leomil72/LM80C/Schematics/LM80C 64K/Kicad/LM80C 64K.sch

## KiCad design Schematics/LM80C 64K/Kicad/LM80C 64K.sch (2021-03-08)

Schematic: LM80C 64K.sch

Parts:
C1, C2, C3, C4, C8, C9, C10, C12, C13, C16, C17, C19, C20, C21, C22, C23, C24, C25, C26, C27, C28, C29, C30, C32, C33, C37, C42: 0.1u; C_Disc_D5.0mm_W2.5mm_P2.50mm
C14, C15: 33p; C_Disc_D5.0mm_W2.5mm_P2.50mm
C18: 220u; CP_Radial_D10.0mm_P2.50mm
C31: 100u; CP_Radial_D5.0mm_P2.00mm
C34, C35: 22p; C_Disc_D5.0mm_W2.5mm_P2.50mm
C36: 100n; C_Disc_D5.0mm_W2.5mm_P2.50mm
C38, C39: 100u; CP_Radial_D4.0mm_P2.00mm
C40, C41: 10u; CP_Radial_D5.0mm_P2.00mm
D1, D3, D5: LED; LED_D5.0mm
D2, D4: 1N4007; D_DO-41_SOD81_P10.16mm_Horizontal
FB1: Ferrite_Bead; LairdTech_28C0236-0JW-10
H1, H2, H3, H4: MountingHole_Pad; MountingHole_3.2mm_M3_Pad
J1: Conn_02x20_Odd_Even; PinHeader_2x20_P2.54mm_Vertical
J2: AV-VIDEO; RCAsimple
J3: Conn_01x03; PinHeader_1x03_P2.54mm_Vertical
J4: Conn_01x12; PinHeader_1x12_P2.54mm_Vertical
J5, J6: Conn_01x08_Male; PinHeader_1x08_P2.54mm_Vertical
J7, J12: FT232 CONN; PinSocket_1x06_P2.54mm_Vertical
J8: Barrel_Jack_Switch; BarrelJack_Horizontal
J9: Conn_01x20; PinHeader_1x20_P2.54mm_Vertical
J10: AV-L AUDIO; RCAsimple
J11: AV-R AUDIO; RCAsimple
JP1: Jumper; PinHeader_1x02_P2.54mm_Vertical
Q1: 2N3904; TO-92_Inline
Q2: BC337; TO-92_Inline
R1, R2, R6, R8, R11, R20, R21, R22, R31, R34, R36, R37, R51: 10K; R_Axial_DIN0207_L6.3mm_D2.5mm_P10.16mm_Horizontal
R3, R5, R32, R33, R35, R48, R49, R55, R56: 2K7; R_Axial_DIN0207_L6.3mm_D2.5mm_P10.16mm_Horizontal
R4, R38, R41, R44, R46, R47, R53: 1K; R_Axial_DIN0207_L6.3mm_D2.5mm_P10.16mm_Horizontal
R7: 470R; R_Axial_DIN0207_L6.3mm_D2.5mm_P10.16mm_Horizontal
R9, R10: 75R; R_Axial_DIN0207_L6.3mm_D2.5mm_P10.16mm_Horizontal
R12, R13, R14, R15, R16, R17, R18, R19: 390R; R_Axial_DIN0207_L6.3mm_D2.5mm_P10.16mm_Horizontal
R23, R24, R25, R26, R27, R28, R29, R30, R54: 330R; R_Axial_DIN0207_L6.3mm_D2.5mm_P10.16mm_Horizontal
R39: 100K; R_Axial_DIN0207_L6.3mm_D2.5mm_P10.16mm_Horizontal
R40: 8M2; R_Axial_DIN0207_L6.3mm_D2.5mm_P10.16mm_Horizontal
R42, R43: 2K2; R_Axial_DIN0207_L6.3mm_D2.5mm_P10.16mm_Horizontal
R45: 330; R_Axial_DIN0207_L6.3mm_D2.5mm_P10.16mm_Horizontal
R50: 47K; R_Axial_DIN0207_L6.3mm_D2.5mm_P10.16mm_Horizontal
R52: 470; R_Axial_DIN0207_L6.3mm_D2.5mm_P10.16mm_Horizontal
SW1: SW_DIP_x01; SW_PUSH_6mm_H4.3mm
U1: 74HCT139; DIP-16_W7.62mm_LongPads
U2: 74HCT138; DIP-16_W7.62mm_LongPads
U3, U22: 74HCT32; DIP-14_W7.62mm_LongPads
U5: Z80-CPU; DIP-40_W15.24mm_LongPads
U6, U7: HM62256BLP-12; DIP-28_W15.24mm_LongPads
U9: 28C256; DIP-28_W15.24mm_LongPads
U10: 74HCT08; DIP-14_W7.62mm_LongPads
U11: Z80-CTC; DIP-28_W15.24mm_LongPads
U12: Z80-PIO; DIP-40_W15.24mm_LongPads
U13: TMS9918A; DIP-40_W15.24mm_LongPads
U14, U15, U16: 74HCT574; DIP-20_W7.62mm_LongPads
U17: ULN2803A; DIP-18_W7.62mm_LongPads
U18: Z80-SIO_0; DIP-40_W15.24mm_LongPads
U19, U23: 74HCT04; DIP-14_W7.62mm_LongPads
U20: HM62256BLP-7; DIP-28_W15.24mm_LongPads
U21: 4066; DIP-14_W7.62mm_LongPads
U24: 74HC02; DIP-14_W7.62mm_LongPads
U25: AY-3-8910; DIP-40_W15.24mm_LongPads
U26: LM317_3PinPackage; TO-220-3_Vertical
U27: NE555P; DIP-8_W7.62mm
U28: 74HCT74; DIP-14_W7.62mm_LongPads
Y1: 10.738635MHz; Crystal_HC49-4H_Vertical
Y2: 7.372800MHz; Crystal_HC49-4H_Vertical

Notes on the sheet:
CLOCK DIVIDER /2: SYSTEM CLOCK IS 3.686400 MHz
POWER REGULATOR (9-12V IN --> 5V OUT)
6: DTR 5: RX 4: TX 3: VCC 2: CTS 1: GND
WARNING! VDP DATA BUS HAS CD0 AS MSB AND CD7 AS LSB!
BE CAREFUL!! VAxx CONNECTIONS BETWEEN D-FFs AND SRAM DON’T FOLLOW THE NUMERICAL ORDER!
COMPOSITE VIDEO OUT
I/O DECODER: 0000xxxx: PIO 0001xxxx: CTC 0010xxxx: SIO 0011xxxx: VDP 0100xxxx: PSG 0101xxxx: CF
CLOCK DIVIDER: CLK2 = 1.832400MHz
Connect to an 8-segment LED bar graph or to 8x LEDs.
MANUAL RESET
Keyboard connector
PSG ADDRESS DECODER: 0100xx00: READ FROM PSG (IN) 0100xx01: WRITE TO PSG (OUT) 0100xx00: LATCH ADDRESS (OUT)
RAM/ROM SELECTOR
Cap values are NOT valid for every crystal. Check the load capacitance of yours
POWER LED
RESET CIRCUIT (0.5s TRIGGER TIME)
SPECIAL FUNCTIONS: PB0: switch for ROM/RAM on bank#1 PB1: switch between bansk #0/1 on VRAM PB4: serial 1 error (disables serial switch) PB6: serial 1 opened (enables serial switch)
NOTE: not implemented in code yet
CONNECT IF YOUR CF/IDE ADAPTER DOES NOT HAVE A BUILT-IN ACTIVITY LED
CF ADAPTER POWER JACK
