leomil72/LM80C/BASIC examples/amiga_hand.bas

10 REM AMIGA BOOT HAND
20 REM WRITTEN BY
30 REM ANTONINO PORCINO 
40 REM 01 OCTOBER 2021
50 REM ORIGINAL SOURCE 
60 REM TAKEN SOMEWHERE 
70 REM FROM INTERNET
80 REM
100 SCREEN 2
200 COLOR 1,15,5
1000 PLOT 107,35
1001 DRAW 107,35,130,35
1002 DRAW 130,35,130,57
1003 DRAW 130,57,185,57
1004 DRAW 185,57,185,35
1005 DRAW 185,35,197,35
1006 DRAW 197,35,208,46
1007 DRAW 208,46,208,118
1008 DRAW 208,118,199,118
1009 DRAW 199,118,199,80
1010 DRAW 199,80,136,80
1011 DRAW 136,80,134,78
1012 DRAW 134,78,125,78
1013 DRAW 125,78,124,80
1014 DRAW 124,80,117,80
1015 DRAW 117,80,117,89
1016 DRAW 117,89,107,96
1017 DRAW 107,96,107,35
1018 REM PAINT 109,93
1019 PLOT 105,96
1020 DRAW 105,96,105,34
1021 DRAW 105,34,198,34
1022 DRAW 198,34,210,46
1023 DRAW 210,46,210,119
1024 DRAW 210,119,158,119
1025 DRAW 158,119,158,124
1026 DRAW 158,124,154,132
1027 DRAW 154,132,150,137
1028 DRAW 150,137,146,140
1029 DRAW 146,140,140,149
1030 DRAW 140,149,132,153
1031 DRAW 132,153,132,164
1032 DRAW 132,164,82,164
1033 DRAW 82,164,82,133
1034 DRAW 82,133,81,133
1035 DRAW 81,133,81,105
1036 DRAW 81,105,85,99
1037 DRAW 85,99,92,93
1038 DRAW 92,93,93,89
1039 DRAW 93,89,97,82
1040 DRAW 97,82,102,79
1041 DRAW 102,79,105,78
1042 DRAW 105,78,105,78
1043 DRAW 105,78,102,80
1044 DRAW 102,80,98,82
1045 DRAW 98,82,94,89
1046 DRAW 94,89,93,93
1047 DRAW 93,93,86,99
1048 DRAW 86,99,82,105
1049 DRAW 82,105,82,132
1050 DRAW 82,132,83,133
1051 DRAW 83,133,83,163
1052 DRAW 83,163,112,163
1053 DRAW 112,163,112,142
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
1167 DRAW 126,125,126,128
1168 PLOT 198,35
1169 DRAW 198,35,209,46
1170 DRAW 209,46,209,118
1171 PAINT 106,35
1172 PAINT 131,35
1173 PAINT 169,39
1174 PAINT 178,51
1175 PAINT 184,39
1176 PAINT 198,118
1177 PAINT 147,120
1178 PAINT 118,81
1200 GPRINT "LM80C",18,12,4
2000 GOTO 2000
