leomil72/LM80C/BASIC examples/graphic_demos.bas

10 A=INKEY(10)
20 SCREEN 2:GPRINT "Press any key for next demo...",1,23
30 DRAW 127,95,RND(1)*256,RND(1)*192,RND(1)*13+1
40 IF INKEY(0)=0 THEN 30
70 CLS:GPRINT "Press RUN/STOP to stop",5,23,15,1
80 FOR I=0 TO 255
90 DRAW 127,95,I,0,RND(1)*13+1:NEXT
100 FOR I=0 TO 191:
110 DRAW 127,95,255,I,RND(1)*13+1:NEXT
120 FOR I=255 TO 0 STEP -1
130 DRAW 127,95,I,191,RND(1)*13+1:NEXT
140 FOR I=191 TO 0 STEP -1
150 DRAW 127,95,0,I,RND(1)*13+1:NEXT
160 GPRINT "Press any key to exit",5,23,1,15
170 A=INKEY(5):IF A=0 THEN 170
180 SCREEN 1
