leomil72/LM80C/BASIC examples/graphic_examples.bas

5 REM GRAPHIC EXAMPLES
6 REM FOR LM80C BASIC
7 REM WRITTEN BY LEONARDO MILIANI
8 REM
10 SCREEN2:VOLUME1,15
20 FOR NR=1TO3
30 ON NR GOSUB 1000,2000,3000
40 SOUND1,3000,10:GPRINT"Press any key...",8,23,1,15:A=INKEY(10)
50 A=INKEY(50):IFA=0THEN50
60 NEXT
998 SCREEN 1
999 END
1000 FORX=-128TO128STEP8:IFX>127THENX=127
1010 DRAW X+128,0,128,96-ABS(INT(X/1.4))
1020 DRAW X+128,191,128,96+ABS(INT(X/1.4))
1030 NEXT
1040 FOR Y=-96TO96STEP8:IFY>95THENY=95
1050 DRAW 0,Y+96,128-ABS(Y),96
1060 DRAW 255,Y+96,128+ABS(Y),96
1070 NEXT
1080 RETURN
2000 CLS
2010 FOR N=0 TO 192 STEP 4
2020 DRAW 0,191,N,0
2030 DRAW 0,0,N,191
2040 DRAW 255,191,255-N,0
2050 DRAW 255,0,255-N,191
2060 NEXT
2070 RETURN
3000 CLS:COLOR10,1,1
3010 FORN=1TO50
3020 DRAW 128,96,INT(RND(1)*256),INT(RND(1)*86+10),10
3030 NEXT
3040 DRAW 0,96,255,96,13
3050 FOR Y=96TO191STEP16
3060 DRAW 128,96,0,Y,13
3070 DRAW 128,96,255,Y,13
3080 NEXT
3090 FOR X=0 TO 255 STEP 16
3100 DRAW 128,96,X,191,13
3110 NEXT
3120 RETURN
