leomil72/LM80C/BASIC examples/gprint.bas

10 REM TEST OF GPRINT IN GRAPHICS 2
15 REM WORKS WITH LM80C BASIC R3.10 AND ABOVE
20 SCREEN 2
30 FOR I=0TO767
40 X=I%32:Y=I#32
50 CH$=CHR$(INT(RND(1)*256))
60 GPRINT CH$,X,Y,INT(RND(1)*15+1),INT(RND(1)*15+1)
70 NEXT
